Ing-Dom/konnekting_knx-rail-system-xl/dev_doc/datasheets/adafruit_products_fabprint.png

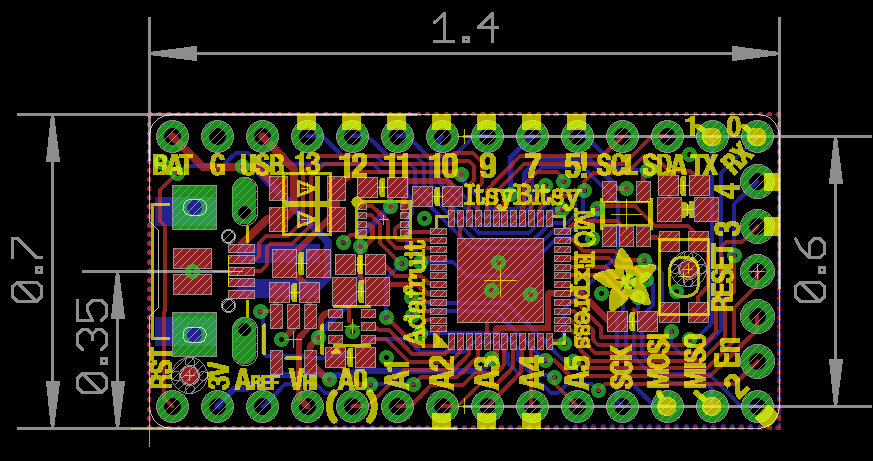
dev_doc/datasheets/adafruit_products_fabprint.png
