Ing-Dom/konnekting_knx-rail-system-xl/dev_doc/datasheets/adafruit_products_schem.png

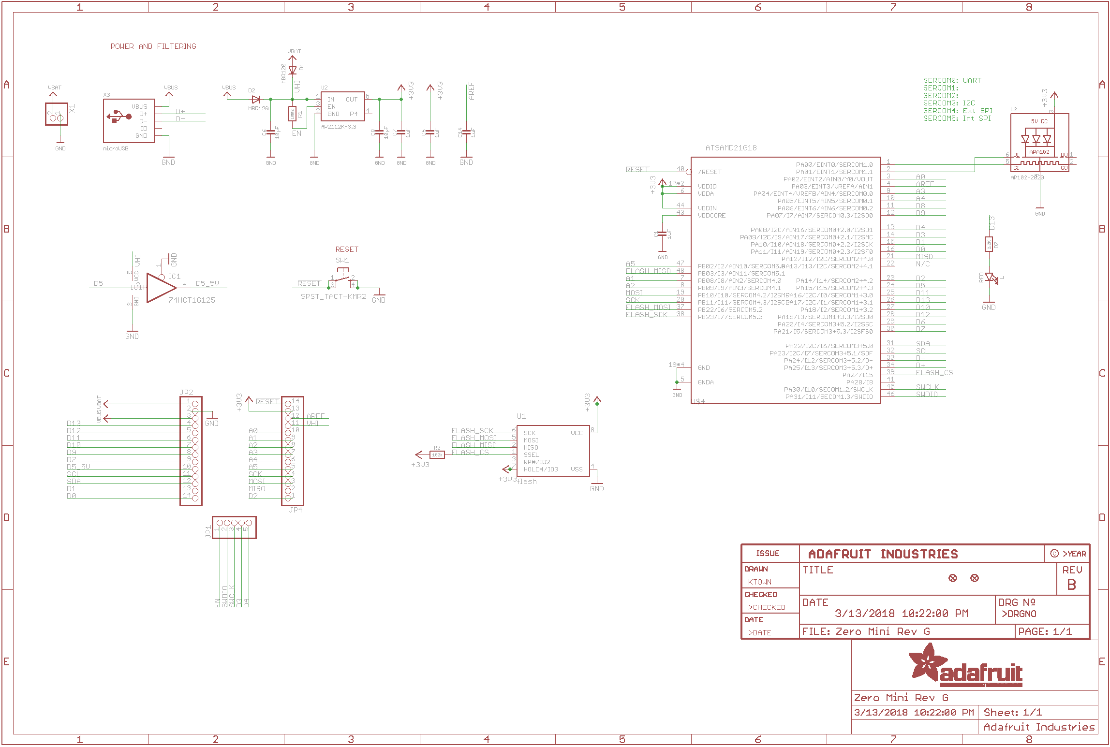
dev_doc/datasheets/adafruit_products_schem.png
