Ing-Dom/konnekting_knx-rail-system-xl/dev_doc/datasheets/wago.jpg

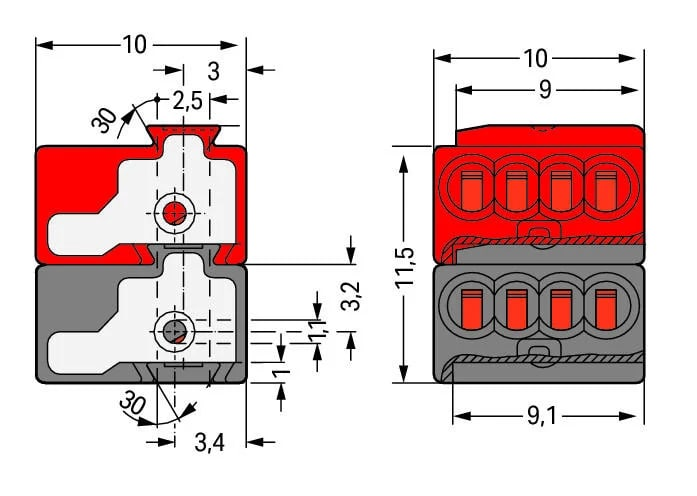
dev_doc/datasheets/wago.jpg
