Ing-Dom/konnekting_knx-rail-system-xl/hardware/KRS-XL_CB6-9-12/EDA-files/KRS-XL_CB6-9-12/KRS-XL_CB6-9-12_V01.00.kicad_pcb-3D Viewer_top.png

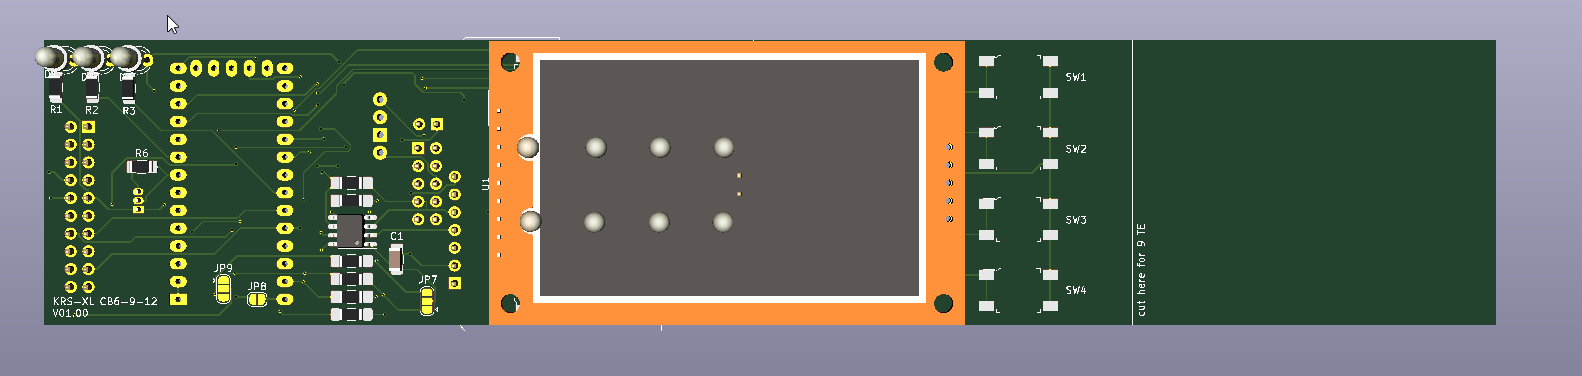
hardware/KRS-XL_CB6-9-12/EDA-files/KRS-XL_CB6-9-12/KRS-XL_CB6-9-12_V01.00.kicad_pcb-3D Viewer_top.png
