Ing-Dom/konnekting_knx-rail-system-xl/hardware/KRS-XL_CB6-9-12/Pictures/IMG_20200124_115416117.jpg

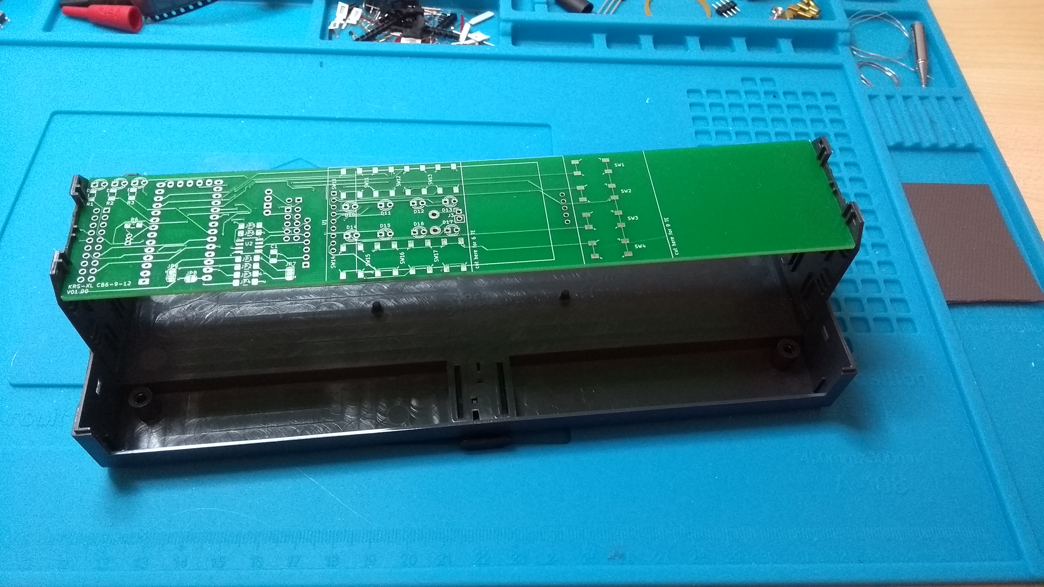
hardware/KRS-XL_CB6-9-12/Pictures/IMG_20200124_115416117.jpg
