Ing-Dom/konnekting_knx-rail-system-xl/hardware/KRS-XL_CB6-9-12/Pictures/IMG_20200126_204340393.jpg

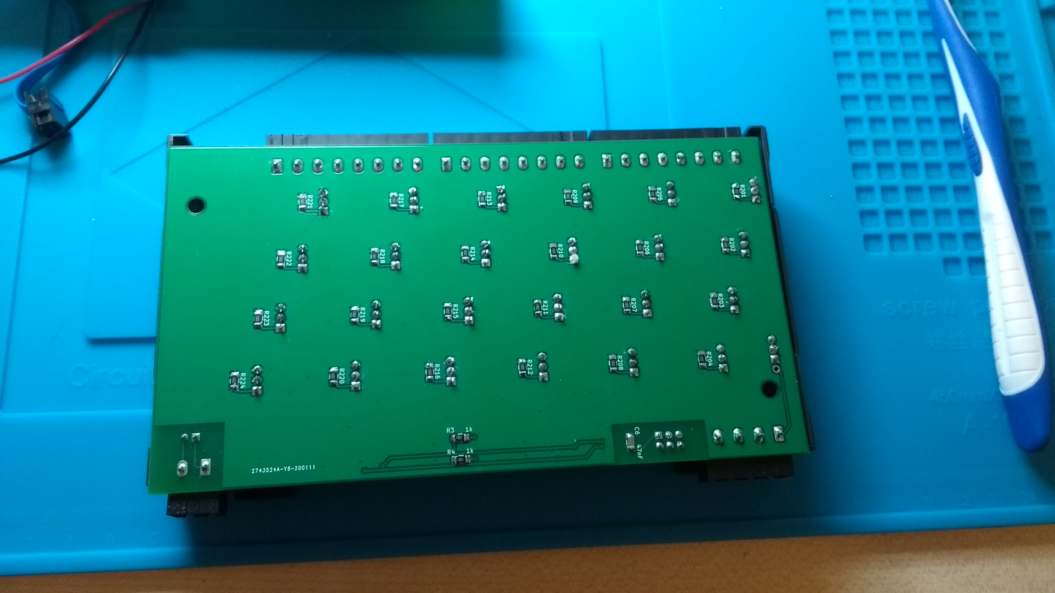
hardware/KRS-XL_CB6-9-12/Pictures/IMG_20200126_204340393.jpg
